knonyks/ATXMEGA256_miniboard/programming/inc/main.h

#ifndef _MAIN_H
#define _MAIN_H

// Hardware configuration
#include "config.h"

// Standard C libraries
#include <stdlib.h>
#include <stdbool.h>

// Standard AVR libraries
#include <avr/io.h>
#include <util/delay.h>
#include <avr/interrupt.h>
#include <avr/sleep.h>
#include <avr/xmega.h>

// External libraries


// External variables


#endif
